DevX-Dragon/OVERRIDE-X3D-Split-Keeb/images/RIGHT ASSEMBLED .png

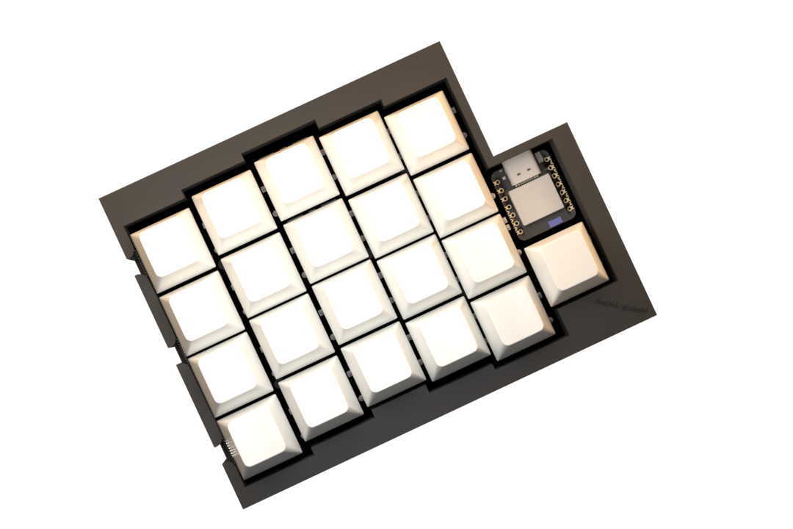
images/RIGHT ASSEMBLED .png
